unkyulee/dr.love/gif/awkward.gif

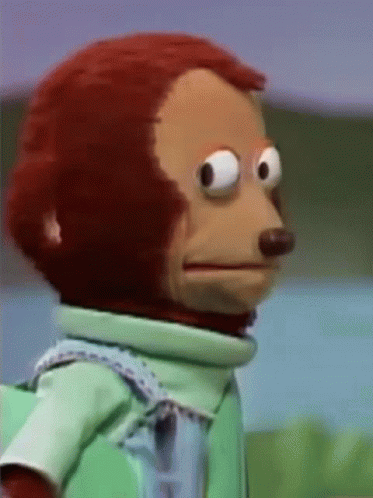
gif/awkward.gif
