unkyulee/dr.love/gif/love love love.gif

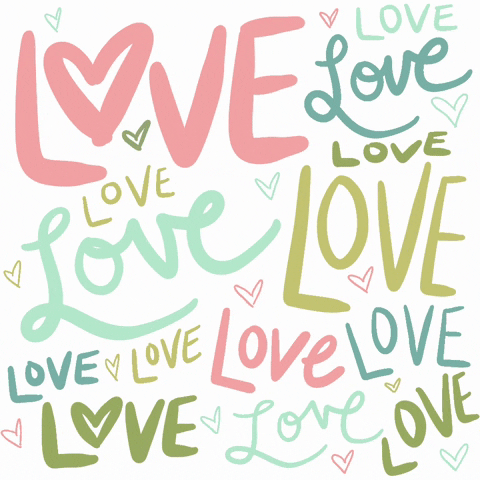
gif/love love love.gif
