unkyulee/dr.love/images/007.jpg

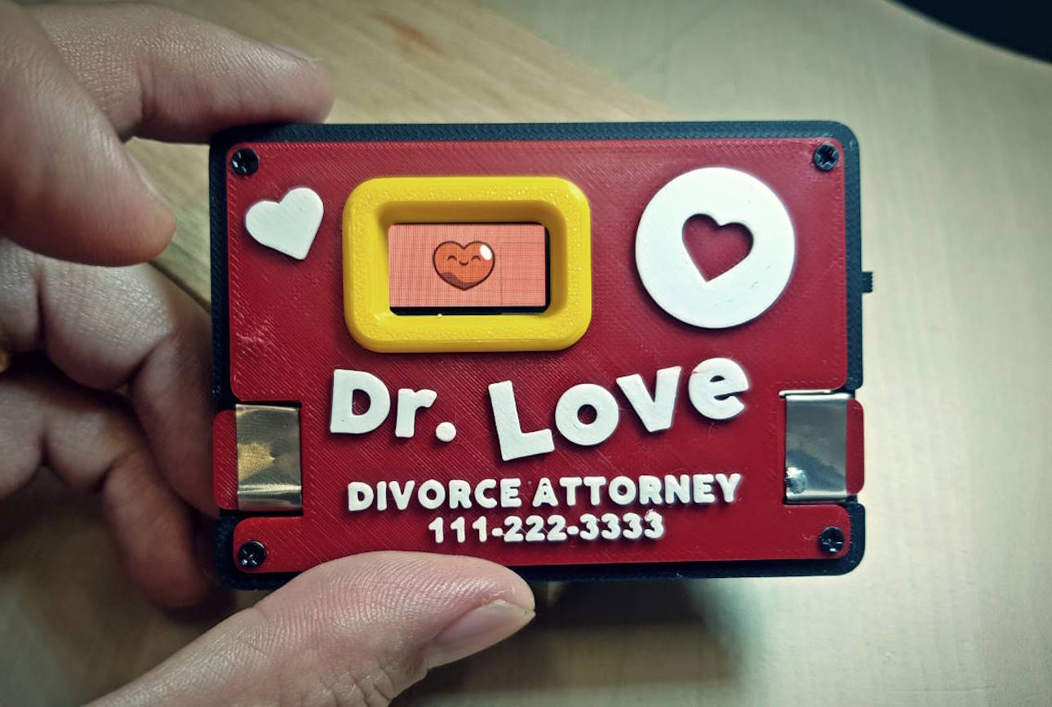
images/007.jpg
